phatvu1294/he-thong-nha-kinh-iot-ung-dung-lora/software/node_co2/main/images.h

// Biểu tượng khởi tạo Lora thành công
#define Lora_icon_width 16
#define Lora_icon_height 16
const unsigned char Lora_icon_bits[] PROGMEM = {
  0x00, 0x7C, 0xCE, 0x00, 0x7C, 0x00, 0x90, 0xB8, 0xB8, 0x90, 0x00, 0x7C, 0x00, 0xFE, 0x38, 0x00,
  0x00, 0x00, 0x00, 0x20, 0x38, 0x1F, 0x1F, 0x08, 0x18, 0x17, 0x3E, 0x38, 0x00, 0x00, 0x00, 0x00
};

// Biểu tượng gửi thành công
#define Send_icon_width 8
#define Send_icon_height 8
const unsigned char Send_icon_bits[] PROGMEM = {
  0x00, 0x20, 0x30, 0x38, 0x38, 0x30, 0x20, 0x00,
};

// Biểu tượng nhận thành công
#define Receive_icon_width 8
#define Receive_icon_height 8
const unsigned char Receive_icon_bits [] PROGMEM = {
  0x00, 0x04, 0x0C, 0x1C, 0x1C, 0x0C, 0x04, 0x00,
};

// Biểu tượng gửi nhận mặc định
#define Default_icon_width 8
#define Default_icon_height 8
const unsigned char Default_icon_bits[] PROGMEM = {
  0x00, 0x00, 0x00, 0x00, 0x00, 0x00, 0x00, 0x00,
};


// Hình sản phẩm
#define Product_bg_width 128
#define Product_bg_height 48
const unsigned char Product_bg_bits[] PROGMEM = {
  0x00, 0x00, 0x00, 0x00, 0x00, 0x00, 0x00, 0x00, 0x00, 0x00, 0x00, 0x00, 0x00, 0x00, 0x00, 0x80,
  0xC0, 0xC0, 0x00, 0x00, 0x60, 0xE0, 0xE0, 0xC7, 0x1F, 0x1E, 0x00, 0xE0, 0xF0, 0x78, 0x1C, 0x00,
  0x00, 0x00, 0x00, 0x00, 0x00, 0x00, 0x00, 0x00, 0x00, 0x00, 0x00, 0x00, 0x00, 0x00, 0x00, 0x00,
  0x00, 0x00, 0x00, 0x00, 0x00, 0x00, 0x00, 0x00, 0x00, 0x00, 0x00, 0x00, 0x00, 0x00, 0x00, 0x00,
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
  0x00, 0x00, 0x00, 0x00, 0x00, 0x00, 0x00, 0x00, 0x00, 0x00, 0x00, 0x00, 0x00, 0x00, 0x00, 0x00,
  0x00, 0x00, 0x00, 0x00, 0x00, 0x00, 0x00, 0x00, 0x00, 0x00, 0x00, 0x00, 0x00, 0x00, 0x01, 0x01,
  0x01, 0x01, 0x01, 0x01, 0x00, 0x00, 0x00, 0x00, 0x00, 0x00, 0x00, 0x00, 0x00, 0x00, 0x00, 0x00
};
